alwaysEpic/pulsar-dreamcast-ble/docs/images/pulsar/edited/controller-back-pulsar.jpg

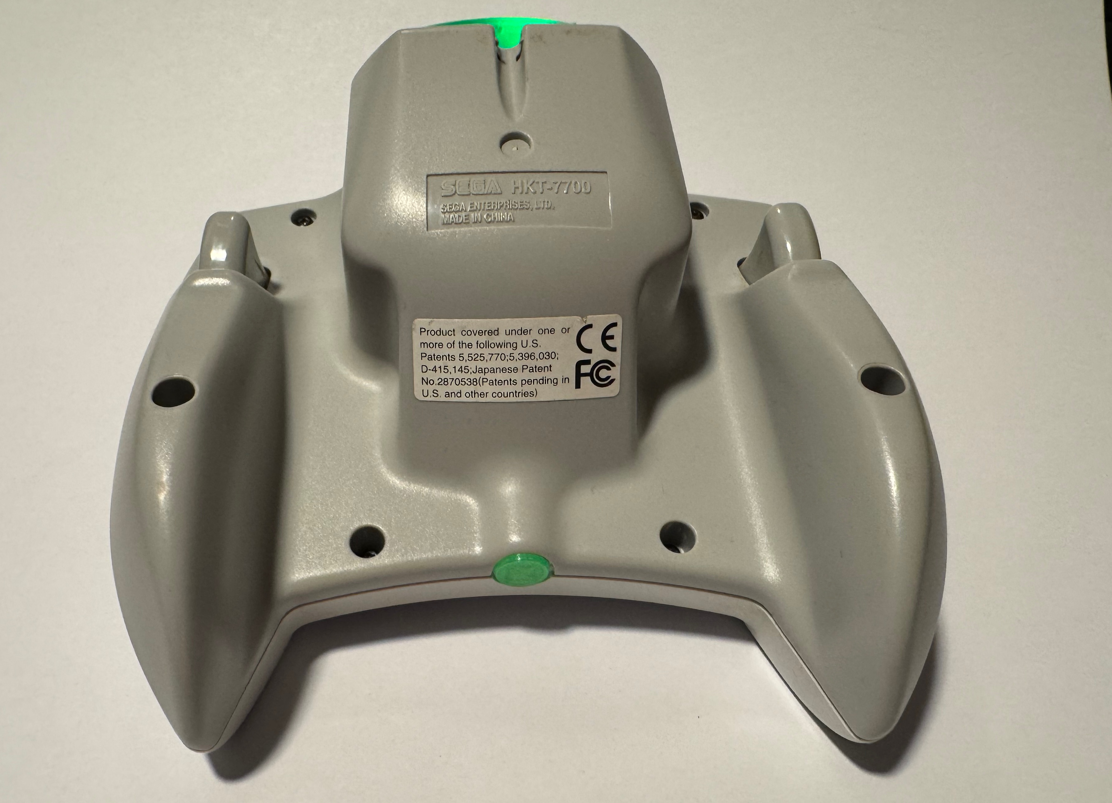
docs/images/pulsar/edited/controller-back-pulsar.jpg
