alwaysEpic/pulsar-dreamcast-ble/docs/images/pulsar/edited/pulsar-device-front.jpg

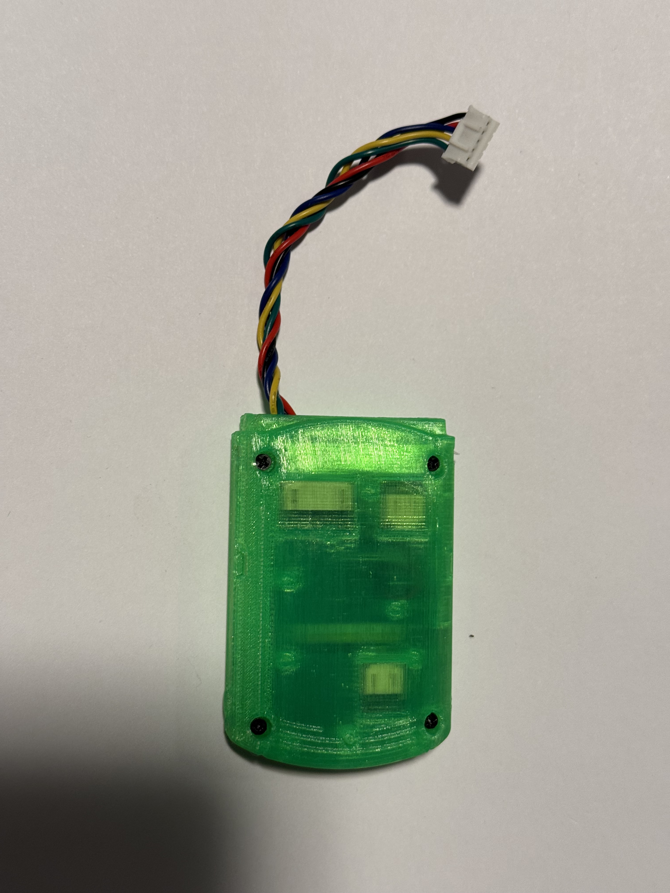
docs/images/pulsar/edited/pulsar-device-front.jpg
