alwaysEpic/pulsar-dreamcast-ble/docs/images/vmu_back.jpeg

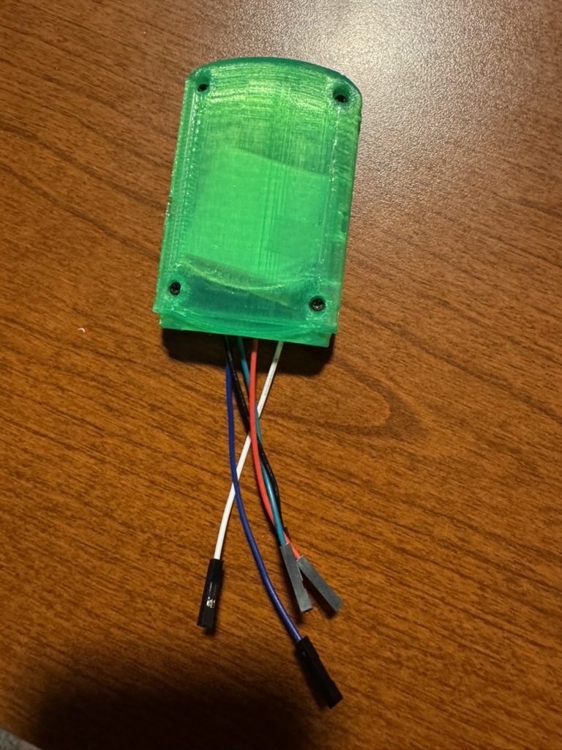
docs/images/vmu_back.jpeg
