alwaysEpic/pulsar-dreamcast-ble/docs/images/vmu_front.jpeg

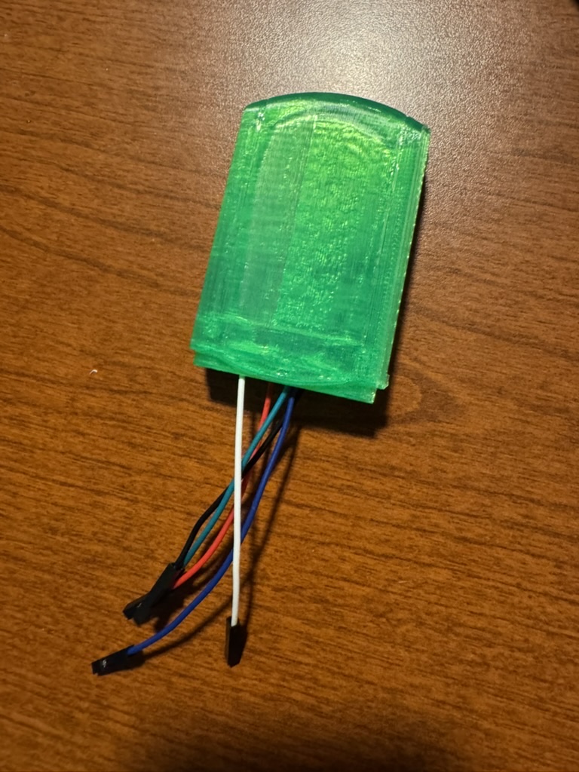
docs/images/vmu_front.jpeg
