alwaysEpic/pulsar-dreamcast-ble/docs/images/vmu_in_controller2.jpeg

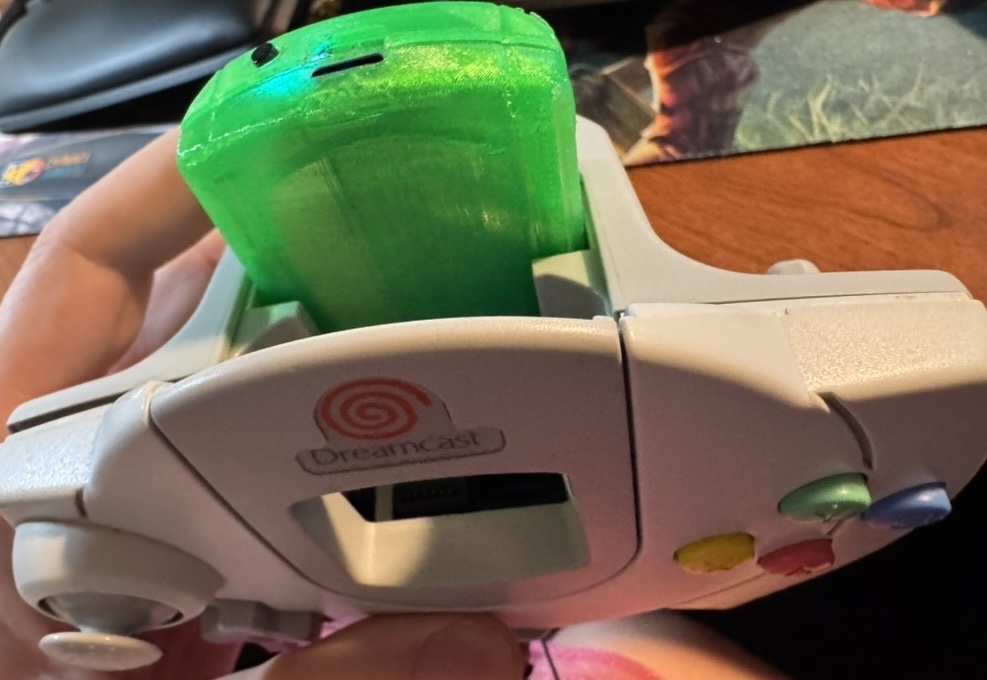
docs/images/vmu_in_controller2.jpeg
