alwaysEpic/pulsar-dreamcast-ble/docs/images/vmu_in_controller.jpeg

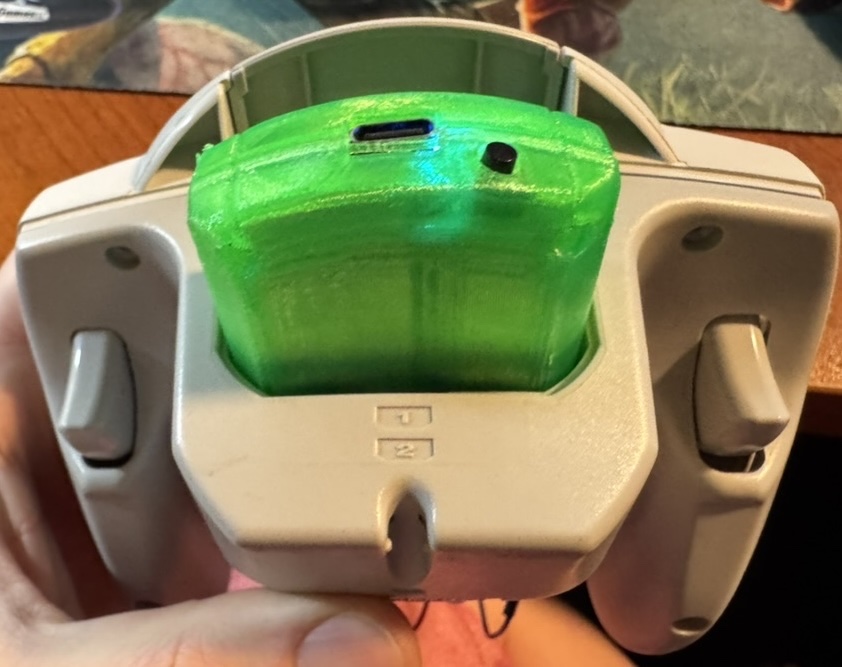
docs/images/vmu_in_controller.jpeg
