alwaysEpic/pulsar-dreamcast-ble/docs/images/vmu_opened2.jpeg

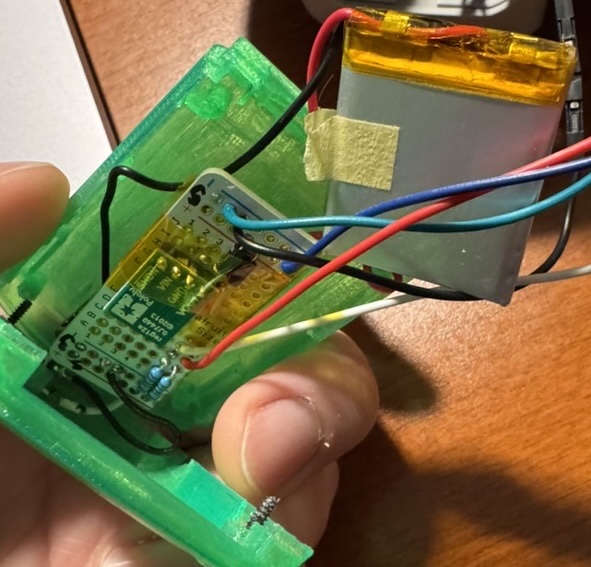
docs/images/vmu_opened2.jpeg
