alwaysEpic/pulsar-dreamcast-ble/docs/signal_references/full_transaction_tx_rx.png

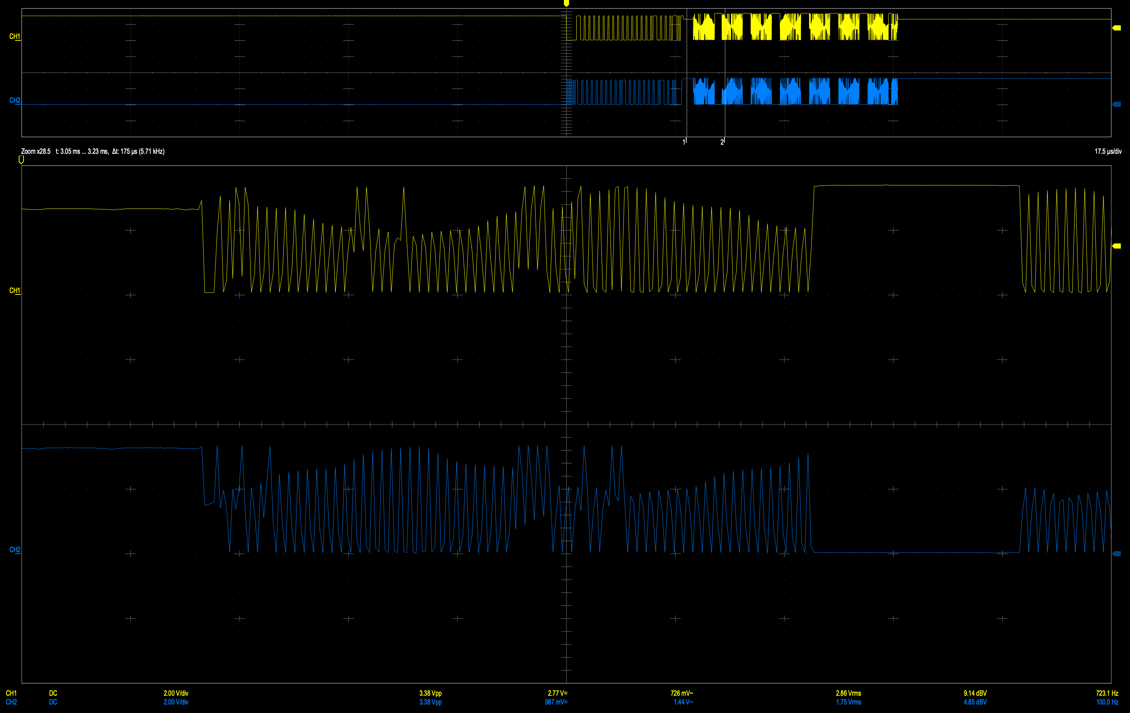
docs/signal_references/full_transaction_tx_rx.png
