alwaysEpic/pulsar-dreamcast-ble/docs/signal_references/response_burst_groups_detail.png

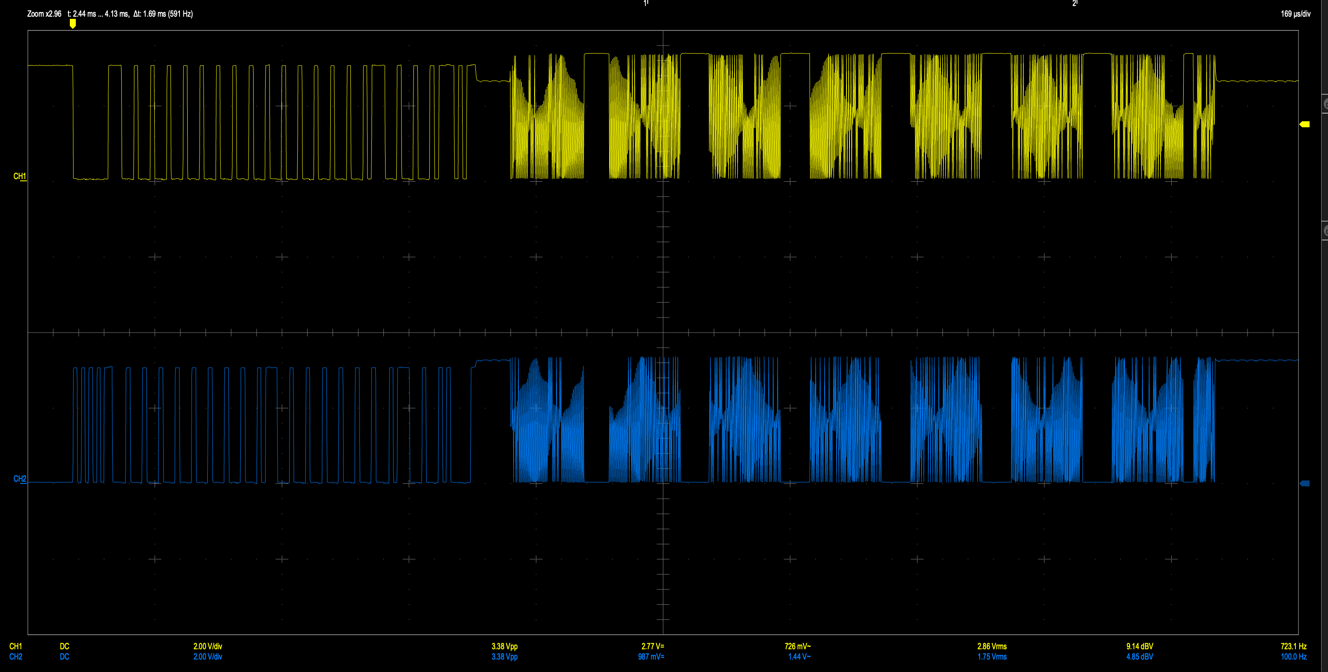
docs/signal_references/response_burst_groups_detail.png
