alwaysEpic/pulsar-dreamcast-ble/hardware/enclosure/VMU_ShellAssembly.step

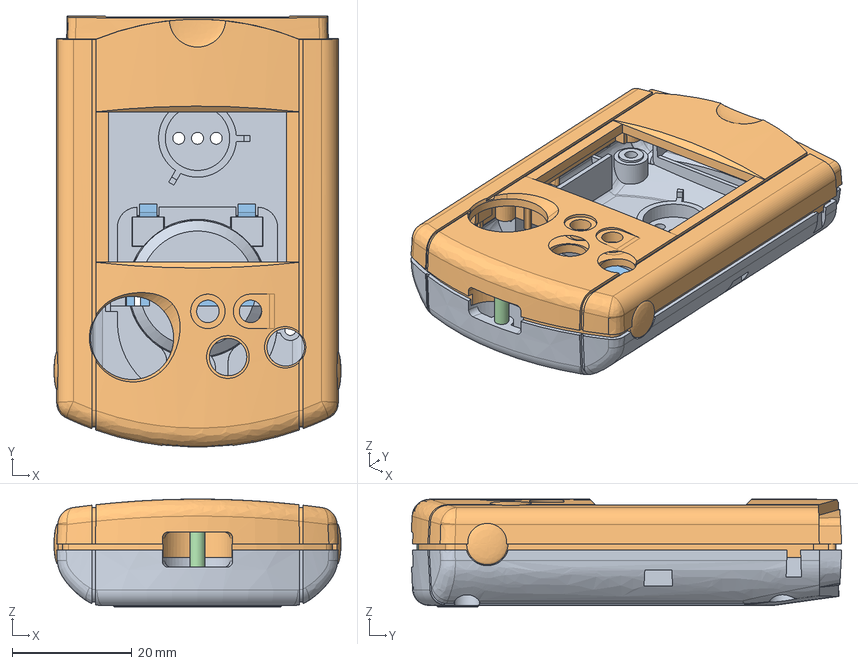
[picture p18: CAD file, 2026-03-05]
hardware/enclosure/VMU_ShellAssembly.step
47.9 x 71.9 x 18.0 mm
VMU_RearShell_1
VMU_FrontShell_1
VMU_BatteryCover
VMU_LanyardPin
