alwaysEpic/pulsar-dreamcast-ble/src/maple/controller_state.rs

// SPDX-License-Identifier: GPL-3.0-or-later
// Copyright 2025-2026 alwaysEpic

//! Dreamcast controller state representation.
//!
//! Re-exports from `maple_protocol` for use within the main embedded crate.

pub use maple_protocol::controller_state::*;
