alwaysEpic/pulsar-dreamcast-ble/src/ble/flash_bond.rs

// SPDX-License-Identifier: GPL-3.0-or-later
// Copyright 2025-2026 alwaysEpic

//! Flash-based bonding storage.
//!
//! Stores BLE bonding data in the last flash page so it persists across power cycles.

#![expect(
    clippy::missing_errors_doc,
    reason = "internal API; the error type is the module's own and has one variant"
)]

use embedded_storage_async::nor_flash::NorFlash;
use nrf_softdevice::ble::{Address, EncryptionInfo, IdentityKey, IdentityResolutionKey, MasterId};
use nrf_softdevice::Flash;

// Compile-time guard: transmute between IdentityResolutionKey and [u8; 16] requires matching size.
const _: () = assert!(core::mem::size_of::<IdentityResolutionKey>() == 16);

/// Flash address for bonding storage. Top page of the app-data window
/// (`0xF1000-0xF3FFF`) that sits directly below the bootloader at `0xF4000`:
/// below Adafruit's region on dev boards, and inside the secure-DFU
/// `NRF_DFU_APP_DATA_AREA` (so OTA updates never erase it) on retail.
/// Moved 2026-08-04 from `0xFE000`, which was the MBR params page.
const BOND_FLASH_ADDR: u32 = 0x000F_3000;

/// Flash page size
const PAGE_SIZE: u32 = 4096;

/// Magic number to identify valid bonding data (V2 schema: integrity-checked,
/// magic written last). Distinct from the V1 magic (`0xB00D_DA7A`) so any V1
/// record — including ones corrupted by a panic mid-save, which V1 could not
/// detect — is discarded on upgrade and the user re-pairs once.
///
/// V1's torn-write hole: `save_bond` wrote the whole record front-to-back,
/// magic first, and `is_valid` checked only the magic. An interrupted save
/// (e.g. the 2026-06-10/11 SoftDevice assert reboot loops, which saved the
/// bond on every reconnect cycle) left valid-magic records with garbage
/// LTK/identity that were then fed to the SoftDevice on every boot.
///
/// V3 (`…DB03`) keeps V2's record layout; only the magic moved. The
/// GATT table was re-laid out and GATT Service Changed removed, so a host
/// bonded before the change could never learn its cached table is stale. A
/// Generic-profile host would reconnect on the unchanged address and read the
/// wrong handles. Discarding every V2 record makes each unit re-pair once.
const BOND_MAGIC: u32 = 0xB00D_DB03;

/// FNV-1a over the record body (everything after `magic` and `crc`), used to
/// reject torn or bit-rotted bond records at load.
fn bond_crc(body: &[u8]) -> u32 {
    let mut hash: u32 = 0x811C_9DC5;
    for &b in body {
        hash ^= u32::from(b);
        hash = hash.wrapping_mul(0x0100_0193);
    }
    hash
}

/// Stored bonding data structure (must be 4-byte aligned for flash writes)
#[repr(C, align(4))]
#[derive(Clone, Copy)]
pub struct StoredBond {
    magic: u32,
    /// FNV-1a over the body (all fields below this one).
    crc: u32,
    /// MasterId.ediv
    ediv: u16,
    /// Padding for alignment
    _pad1: u16,
    /// MasterId.rand (8 bytes)
    rand: [u8; 8],
    /// EncryptionInfo.ltk (16 bytes)
    ltk: [u8; 16],
    /// EncryptionInfo.flags
    enc_flags: u8,
    /// Address flags
    addr_flags: u8,
    /// Padding
    _pad2: u16,
    /// Address bytes (6 bytes)
    addr_bytes: [u8; 6],
    /// Padding
    _pad3: u16,
    /// IRK (16 bytes)
    irk: [u8; 16],
    /// `sys_attrs` length
    sys_attrs_len: u8,
    /// Padding
    _pad4: [u8; 3],
    /// `sys_attrs` data (64 bytes max)
    sys_attrs: [u8; 64],
}

/// Size of the header (magic + crc) preceding the integrity-checked body.
const BOND_HEADER_LEN: usize = 8;

impl StoredBond {
    /// Byte view of the body — every field after the magic/crc header.
    const fn body_bytes(&self) -> &[u8] {
        #[expect(
            clippy::multiple_unsafe_ops_per_block,
            reason = "the offset and the slice construction are one derivation; the \
                      layout argument above is what makes both sound"
        )]
        // SAFETY: `Self` is `repr(C, align(4))`, so its layout is fixed and the
        // header occupies exactly the first `BOND_HEADER_LEN` bytes. Offsetting
        // by that much stays within the same object, and the length is the exact
        // remainder, so the slice cannot run past the struct. The borrow of
        // `self` keeps the memory alive and immutable for the returned slice's
        // lifetime, and `u8` imposes no alignment requirement.
        unsafe {
            core::slice::from_raw_parts(
                core::ptr::from_ref(self).cast::<u8>().add(BOND_HEADER_LEN),
                core::mem::size_of::<Self>() - BOND_HEADER_LEN,
            )
        }
    }

    /// Check if the stored data is valid: magic AND body integrity. A torn
    /// save can never pass — the header (with the magic) is written after
    /// the body, and the crc rejects any partial body.
    #[must_use]
    pub fn is_valid(&self) -> bool {
        self.magic == BOND_MAGIC && self.crc == bond_crc(self.body_bytes())
    }
}

/// Read bonding data from flash
#[must_use]
pub fn load_bond() -> Option<(MasterId, EncryptionInfo, IdentityKey, &'static [u8])> {
    // SAFETY: BOND_FLASH_ADDR is a valid, aligned flash address within the
    // nRF52840 memory map. The StoredBond struct is repr(C, align(4)).
    let stored = unsafe { &*(BOND_FLASH_ADDR as *const StoredBond) };

    if !stored.is_valid() {
        return None;
    }

    let master_id = MasterId {
        ediv: stored.ediv,
        rand: stored.rand,
    };

    let enc_info = EncryptionInfo {
        ltk: stored.ltk,
        flags: stored.enc_flags,
    };

    // Reconstruct Address directly from stored fields
    let addr = Address {
        flags: stored.addr_flags,
        bytes: stored.addr_bytes,
    };

    // SAFETY: IdentityResolutionKey is repr(C) containing only [u8; 16].
    // transmute enforces equal sizes at compile time.
    let irk: IdentityResolutionKey =
        unsafe { core::mem::transmute::<[u8; 16], IdentityResolutionKey>(stored.irk) };

    let peer_id = IdentityKey { irk, addr };

    // Return sys_attrs slice
    let sys_attrs_len = usize::from(stored.sys_attrs_len);
    let sys_attrs = if sys_attrs_len > 0 && sys_attrs_len <= 64 {
        // SAFETY: Length is bounds-checked above (1..=64). Pointer comes from
        // a valid static flash reference with lifetime 'static.
        unsafe { core::slice::from_raw_parts(stored.sys_attrs.as_ptr(), sys_attrs_len) }
    } else {
        &[]
    };

    Some((master_id, enc_info, peer_id, sys_attrs))
}

/// Clear bonding data from flash.
///
/// Not called on entry to pairing mode any more — the bond is retained through
/// the window and replaced only on a successful `on_bonded`.
pub async fn clear_bond(flash: &mut Flash) -> Result<(), ()> {
    // Erase the flash page - this invalidates the magic number
    flash
        .erase(BOND_FLASH_ADDR, BOND_FLASH_ADDR + PAGE_SIZE)
        .await
        .map_err(|_| ())
}

/// Save bonding data to flash
pub async fn save_bond(
    flash: &mut Flash,
    master_id: &MasterId,
    enc_info: &EncryptionInfo,
    peer_id: &IdentityKey,
    sys_attrs: &[u8],
) -> Result<(), ()> {
    // Prepare the data structure
    let mut stored = StoredBond {
        magic: BOND_MAGIC,
        crc: 0,
        ediv: master_id.ediv,
        _pad1: 0,
        rand: master_id.rand,
        ltk: enc_info.ltk,
        enc_flags: enc_info.flags,
        addr_flags: peer_id.addr.flags,
        _pad2: 0,
        addr_bytes: peer_id.addr.bytes,
        _pad3: 0,
        // SAFETY: IdentityResolutionKey is repr(C) containing only [u8; 16].
        irk: unsafe { core::mem::transmute::<IdentityResolutionKey, [u8; 16]>(peer_id.irk) },
        #[expect(
            clippy::cast_possible_truncation,
            reason = "the length is clamped with .min(64) immediately before the cast, and the field it fills is a 64-byte buffer"
        )]
        sys_attrs_len: sys_attrs.len().min(64) as u8,
        _pad4: [0u8; 3],
        sys_attrs: [0u8; 64],
    };
    let copy_len = sys_attrs.len().min(64);
    stored.sys_attrs[..copy_len].copy_from_slice(&sys_attrs[..copy_len]);
    stored.crc = bond_crc(stored.body_bytes());

    // Erase the flash page first
    flash
        .erase(BOND_FLASH_ADDR, BOND_FLASH_ADDR + PAGE_SIZE)
        .await
        .map_err(|_| ())?;

    // SAFETY: StoredBond is repr(C, align(4)) with no padding invariants.
    // Pointer is valid for the struct's size, and the slice doesn't outlive `stored`.
    let data = unsafe {
        core::slice::from_raw_parts(
            (&raw const stored).cast::<u8>(),
            core::mem::size_of::<StoredBond>(),
        )
    };

    // Body first, header (crc + magic) last: a save interrupted at ANY point
    // leaves either an erased page (magic = 0xFFFF_FFFF) or a header-less
    // body — both rejected at load. The V1 layout wrote the magic first,
    // which let panic-interrupted saves produce valid-looking garbage bonds
    // that were re-fed to the SoftDevice on every boot.
    #[expect(
        clippy::cast_possible_truncation,
        reason = "BOND_HEADER_LEN is a compile-time constant of 8, far inside u32"
    )]
    let header_len = BOND_HEADER_LEN as u32;
    flash
        .write(BOND_FLASH_ADDR + header_len, &data[BOND_HEADER_LEN..])
        .await
        .map_err(|_| ())?;
    flash
        .write(BOND_FLASH_ADDR, &data[..BOND_HEADER_LEN])
        .await
        .map_err(|_| ())?;

    Ok(())
}
